chadharrington/all_spark_cube/fpga/led_controller.v

module led_controller
  (
   input         clk,
   input         reset_n,
   input         test_panel_select_n,
   input [31:0]  chunk_data,
   input [3:0]   chunk_addr,
   input         chunk_write_enable,
   input [3:0]   row_addr,
   input [1:0]   panel_addr,
   output        serial_clk,
   output        latch_enable,
   output        output_enable_n,
   output [11:0] serial_data_out,
   output [15:0] row_select_n
   );

   wire          load, load_led_vals, load_brightness, shift;
   wire [17:0]   count;
   wire [6:0]    driver_step;
   wire [7:0]    pwm_time;
   wire [3:0]    active_row_addr;
   wire [3:0]    panel_select;

   
   assign driver_step = count[5:0];
   assign pwm_time = count[13:6];
   assign active_row_addr = count[17:14];

   rom control_rom
     (.clk(clk), .reset_n(reset_n), .addr(driver_step),
      .load(load), .shift(shift), .sclk(serial_clk), 
      .output_enable_n(output_enable_n), .latch_enable(latch_enable));

   binary_counter #(.N(18), .MAX_COUNT(2**18-1)) counter
     (.clk(clk), .reset_n(reset_n), .count(count));

   decoder #(.WIDTH(2)) panel_addr_decoder
     (.addr(panel_addr), .y(panel_select));
   
   inverting_decoder #(.WIDTH(4)) row_driver_decoder
     (.addr(active_row_addr), .y_n(row_select_n));


   genvar        i;
   generate
      for (i=0; i<4; i=i+1)
        begin : panel_drivers
           panel_driver panel_driver_instance
             (.clk(clk), 
              .reset_n(reset_n),
              .test_panel_select_n(test_panel_select_n),
              .shift(shift), 
              .load_led_vals(load), 
              .load_brightness(1'b0), // not using brightness
              .pwm_time(pwm_time),
              .chunk_data(chunk_data),
              .chunk_addr(chunk_addr),
              .chunk_write_enable(panel_select[i] & chunk_write_enable),
              .row_addr(row_addr),
              .active_row_addr(active_row_addr),
              .serial_data_out({serial_data_out[i*3], 
                                serial_data_out[i*3+1], 
                                serial_data_out[i*3+2]}));
        end
   endgenerate

endmodule // controller
