chadharrington/all_spark_cube/fpga/register.v

module register
  #(parameter WIDTH = 1)
   (
    input                  clk,
    input                  reset_n,
    input [WIDTH-1:0]      d,
    output reg [WIDTH-1:0] q
    );

   always @(posedge clk, negedge reset_n)
     if (!reset_n)
       q <= {WIDTH {1'b0}};
     else
       q <= d;

endmodule // register
