chadharrington/all_spark_cube/fpga/binary_counter.v

module binary_counter
  #(parameter N=8, MAX_COUNT=255)
   (
    input clk,
    input reset_n,
    output [N-1:0] count
   );

   reg [N-1:0]     count_reg, next_count;

   always @(posedge clk, negedge reset_n)
     if (!reset_n) 
       count_reg <= 0;
     else
       count_reg <= next_count;

   always @(*)
     begin
        next_count = count_reg + 1'b1;
        if (next_count > MAX_COUNT)
          next_count = 0;
     end

   assign count = count_reg;

endmodule // binary_counter
